Stoyan-Zlatev/SpecialCar/Images/20200710_133950.jpg

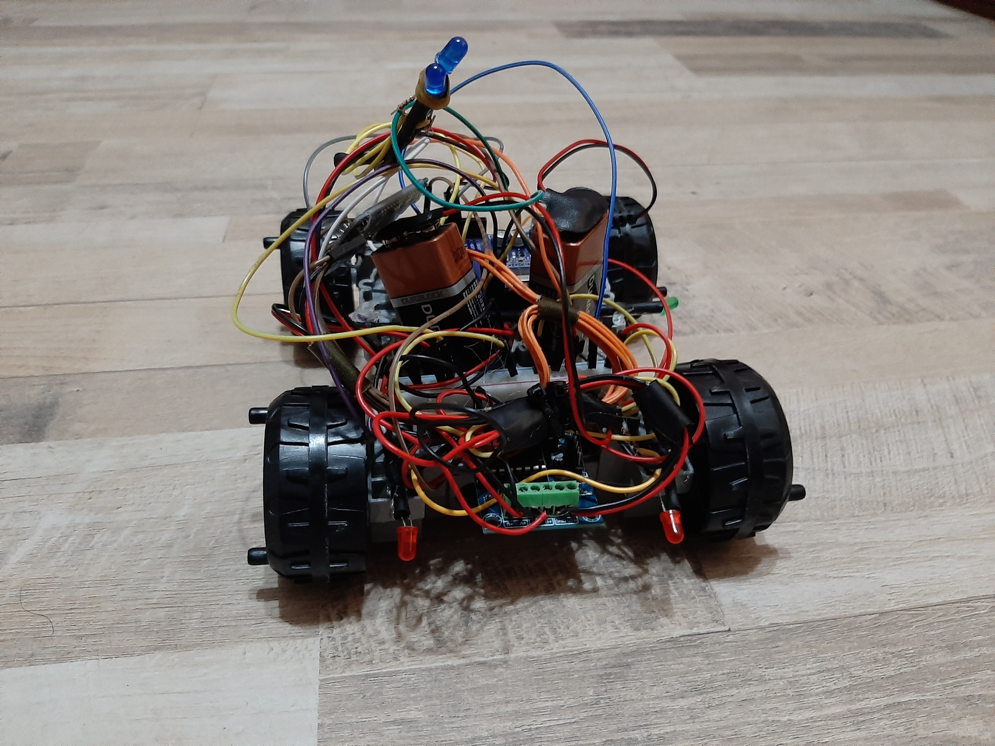
Images/20200710_133950.jpg
