Stoyan-Zlatev/SpecialCar/Images/20200710_134003.jpg

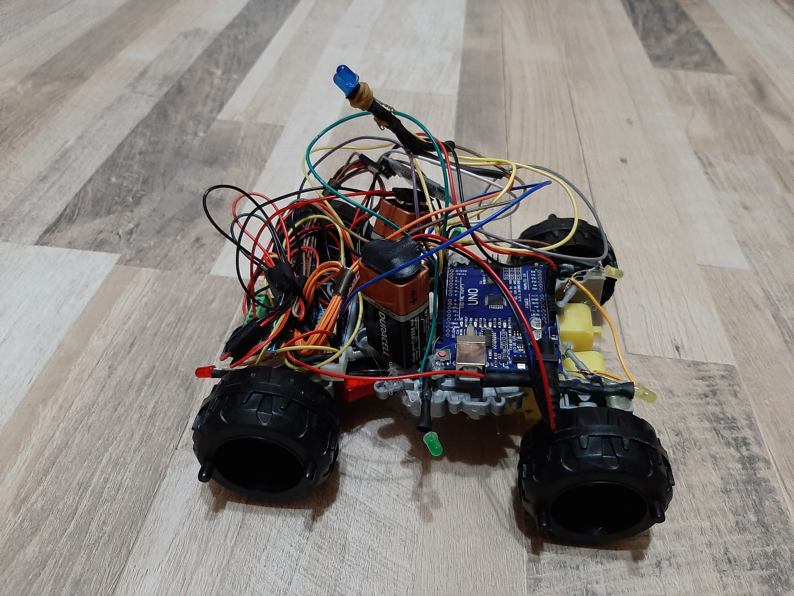
Images/20200710_134003.jpg
