Stoyan-Zlatev/SpecialCar/Images/20200710_134032.jpg

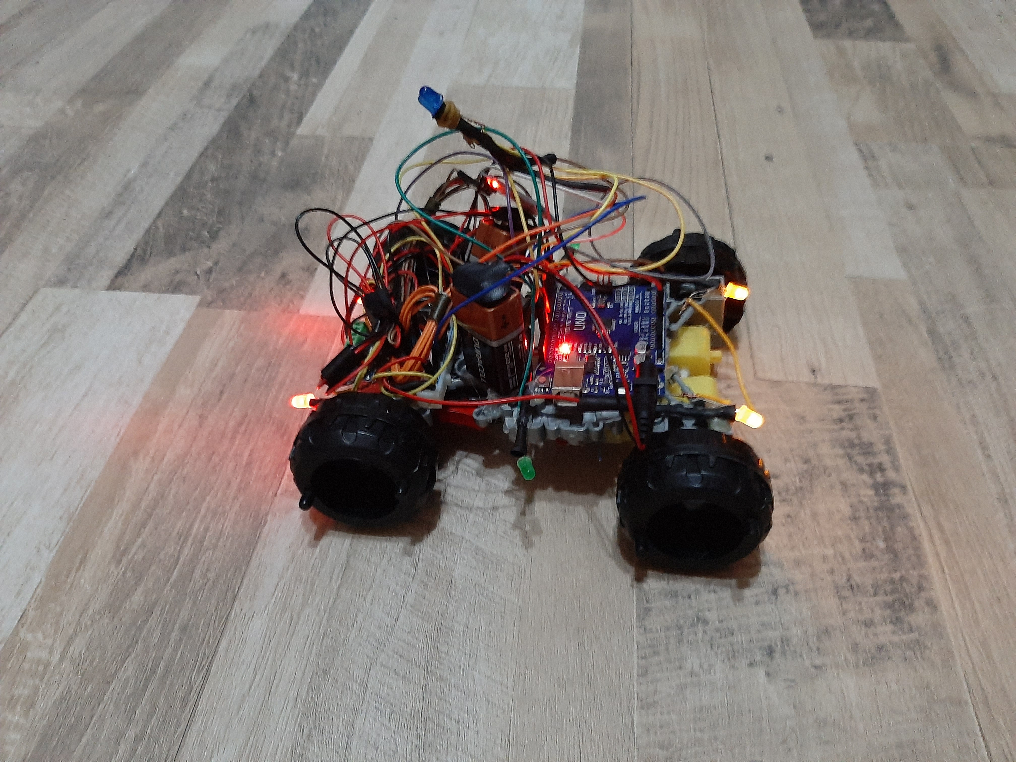
Images/20200710_134032.jpg
