Stoyan-Zlatev/SpecialCar/Images/20200710_134047.jpg

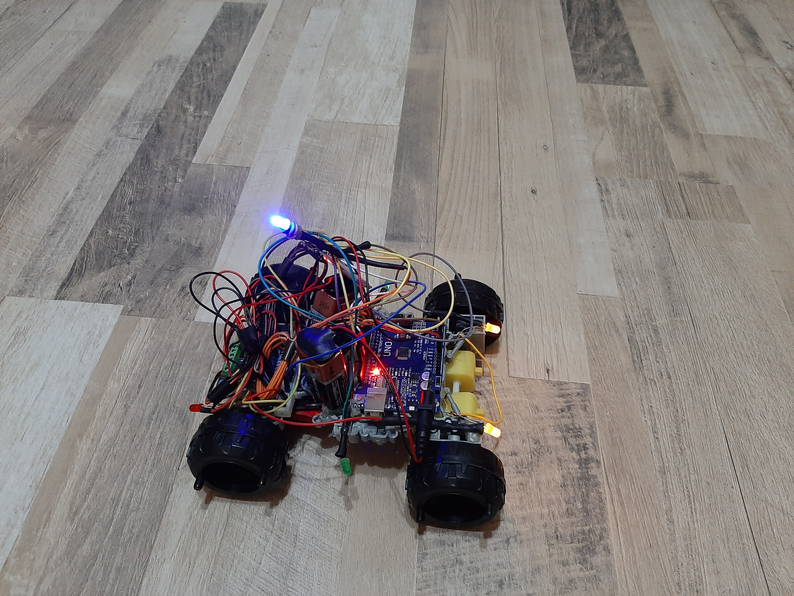
Images/20200710_134047.jpg
