Stoyan-Zlatev/SpecialCar/Images/Electrical Schema.png

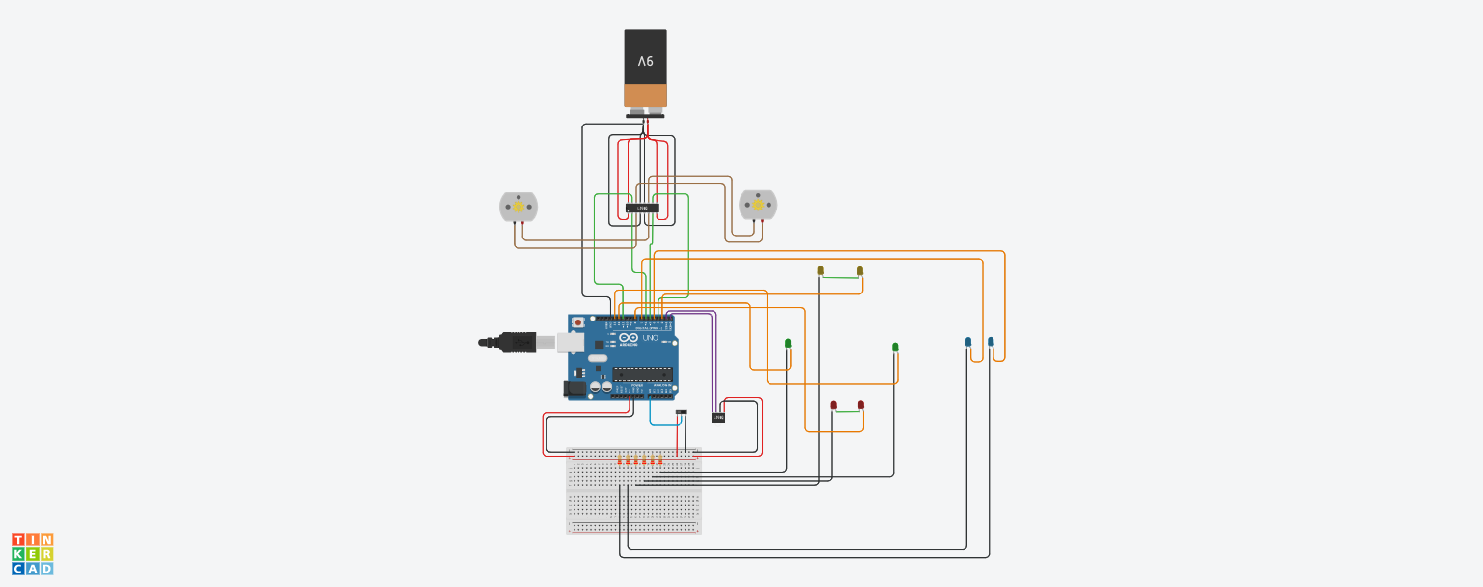
Images/Electrical Schema.png
